Choccy-vr/Modpad/CAD/Knobs.step

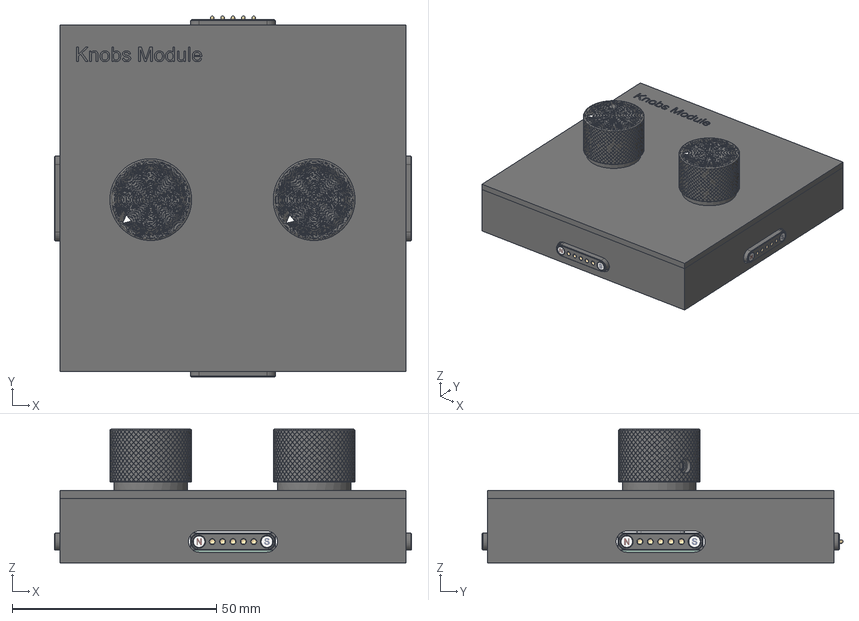
[picture p7: CAD file, 2026-10-07]
CAD/Knobs.step
87.5 x 88.4 x 32.8 mm
R_0805_2012Metric_1
C_0805_2012Metric_1 x 4
TSSOP-20_4.4x6.5mm_P0.65mm_1
SOT-23-3_1
knoED99_silkscreen
knoED99_silkscreen_1
knoED99_PCB
Lb7 x 2
20F x 2
EC11-Housing-THT x 2
Magnetic Pogo Connector 5 Pin (Type 4)
Magnetic Pogo Connector 5 Pin (Type 3) x 3
Knobs_Housing
EC11 Encoder Knob x 2
