Choccy-vr/Modpad/Firmware/ModPad-Firmware-Main/src/Configurator/Configurator.h

#pragma once

#include <Arduino.h>

namespace ModpadConfigurator
{
    // Sets a Binding in the keymap
    bool setKeymapBinding(const char *moduleName, size_t index, uint16_t code, uint8_t modifiers, bool consumer);
    // Sends all Bindings to the configurator
    void sendAllKeymapsJson();
    // Sends which modules are active
    void sendActiveModulesJson();
    // Sends press notification
    void sendPressNotificationJson(const char *moduleName, uint8_t index, bool encoder);
    // Sends a debug message, keeps the serial stream pure JSON
    void sendLogJson(const String &msg);
    // Processes Configurator Command
    void processConfigCommand(const String &payload);
    // Non-blocking serial listener
    void processConfiguratorSerial();

}
